cegea/rf_remote_homeassistant/src/remote_rf_w_mqtt_client/remote_rf_w_mqtt_client.h

#ifndef remote_rf_w_mqtt_client_h
#define remote_rf_w_mqtt_client_h

#include "secrets.h"
#include "remote_rf.h"

#if !( defined(ARDUINO_RASPBERRY_PI_PICO_W) )
  #error For RASPBERRY_PI_PICO_W only
#endif

// Debug Level from 0 to 4
#define _ASYNCTCP_RP2040W_LOGLEVEL_         1
#define _ASYNC_MQTT_LOGLEVEL_               1

#if (_ASYNC_MQTT_LOGLEVEL_ > 3)
  #warning Using RASPBERRY_PI_PICO_W with CYC43439 WiFi
#endif

// RP2040 pins SPI0
#define SCK 2
#define MISO 4
#define MOSI 3
#define SS 5
#define GDO0 7
#define GDO2 6

// secrets.h:
// #define WIFI_SSID         "name"    // your network SSID (name)
// #define WIFI_PASSWORD     "passwd"    // your network password (use for WPA, or use as key for WEP), length must be 8+

// #define MQTT_USER         "user";
// #define MQTT_CREDENTIALS  "credentials";


#endif    //remote_rf_w_mqtt_client_h
